Prakhar730/AHRS_PCB_Design/Power Supply Simulation/Draft1.asc

C1: cap; 10µ
C2: cap; 22µ
L1: ind; 2.2µ
R1: res; 100k
R2: res; 6.6
U1: TPS62172_TRANS
V1: voltage; 5
Named nets: 0
.tran 1ms startup
